MVeszpremi/M202_Solar_Tracker/data/image/3.jpg

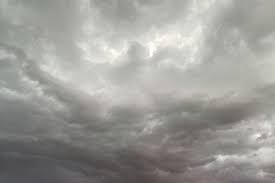
data/image/3.jpg
