MVeszpremi/M202_Solar_Tracker/data/image/7.jpg

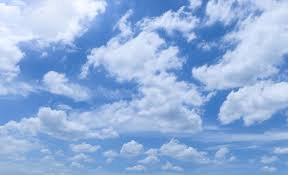
data/image/7.jpg
