MVeszpremi/M202_Solar_Tracker/data/image/8.jpg

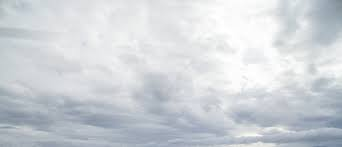
data/image/8.jpg
