MVeszpremi/M202_Solar_Tracker/data/image/10.jpg

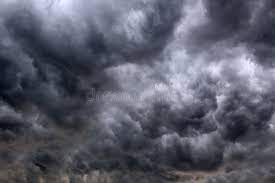
data/image/10.jpg
