MVeszpremi/M202_Solar_Tracker/data/image/11.jpg

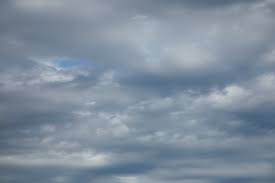
data/image/11.jpg
