MVeszpremi/M202_Solar_Tracker/data/image/12.jpg

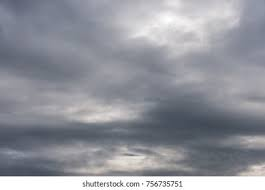
data/image/12.jpg
