MVeszpremi/M202_Solar_Tracker/data/image/13.jpg

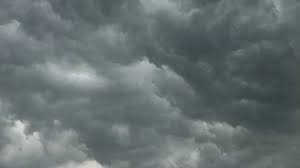
data/image/13.jpg
