MVeszpremi/M202_Solar_Tracker/data/image/14.jpg

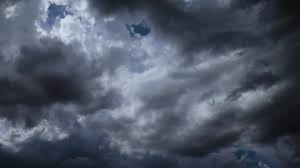
data/image/14.jpg
