MVeszpremi/M202_Solar_Tracker/data/image/15.jpg

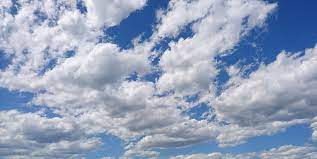
data/image/15.jpg
