MVeszpremi/M202_Solar_Tracker/data/image/16.jpg

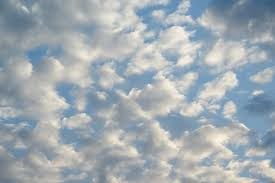
data/image/16.jpg
