MVeszpremi/M202_Solar_Tracker/data/image/17.jpg

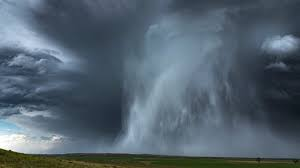
data/image/17.jpg
