MVeszpremi/M202_Solar_Tracker/data/image/19.jpg

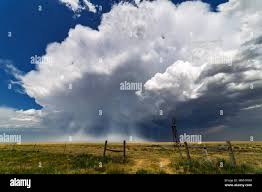
data/image/19.jpg
