MVeszpremi/M202_Solar_Tracker/data/image/20.jpg

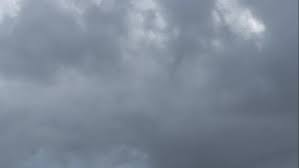
data/image/20.jpg
