MVeszpremi/M202_Solar_Tracker/data/image/sunny1.jpg

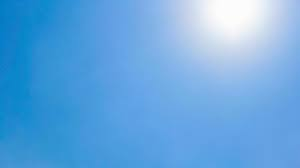
data/image/sunny1.jpg
