MVeszpremi/M202_Solar_Tracker/data/image/sunny2.jpg

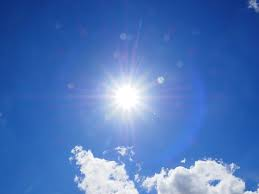
data/image/sunny2.jpg
