MVeszpremi/M202_Solar_Tracker/data/image/sunny4.jpg

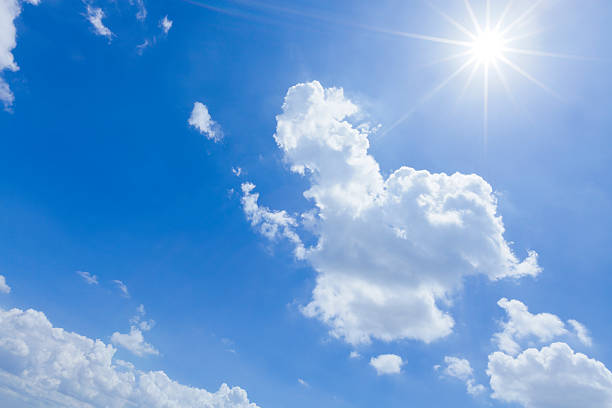
data/image/sunny4.jpg
