MVeszpremi/M202_Solar_Tracker/data/image/sunny5.jpg

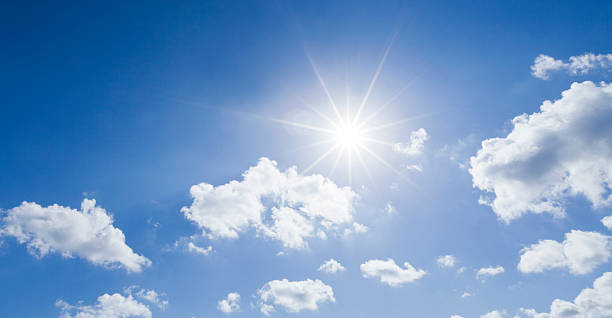
data/image/sunny5.jpg
