MVeszpremi/M202_Solar_Tracker/data/image/sunny6.jpg

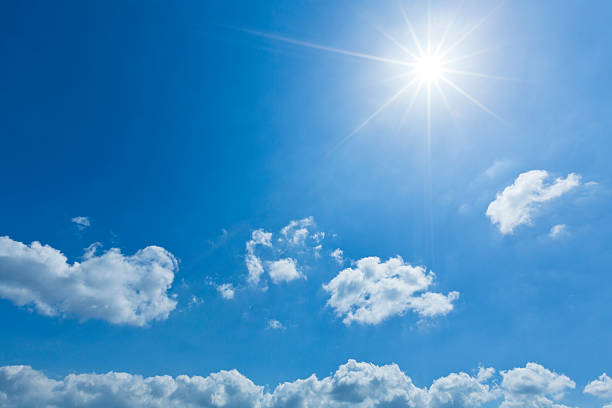
data/image/sunny6.jpg
