MVeszpremi/M202_Solar_Tracker/data/image/sunny7.jpg

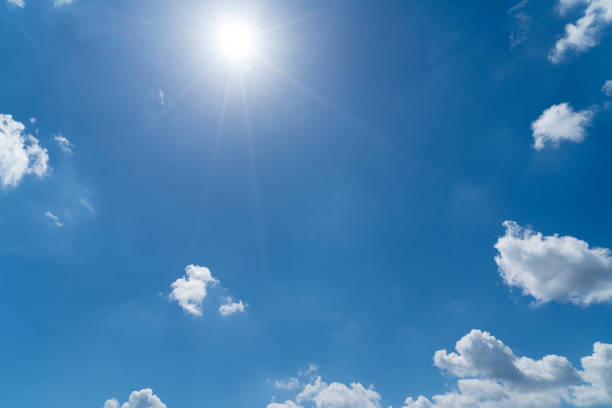
data/image/sunny7.jpg
