MVeszpremi/M202_Solar_Tracker/data/image/sunny8.jpg

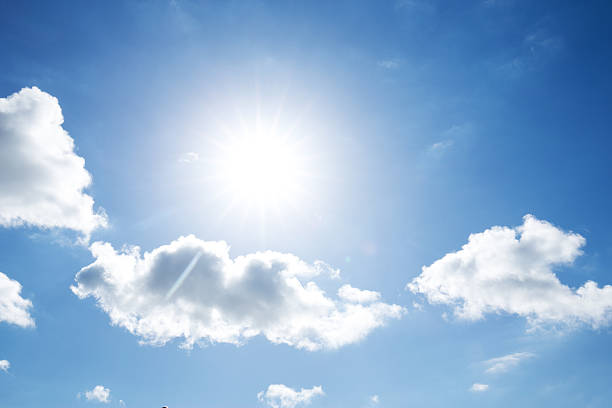
data/image/sunny8.jpg
