MVeszpremi/M202_Solar_Tracker/data/image/sunny9.jpg

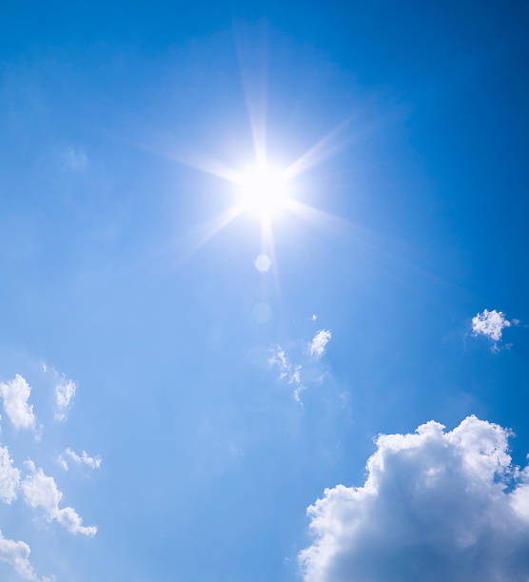
data/image/sunny9.jpg
