MVeszpremi/M202_Solar_Tracker/data/image/sunny10.jpg

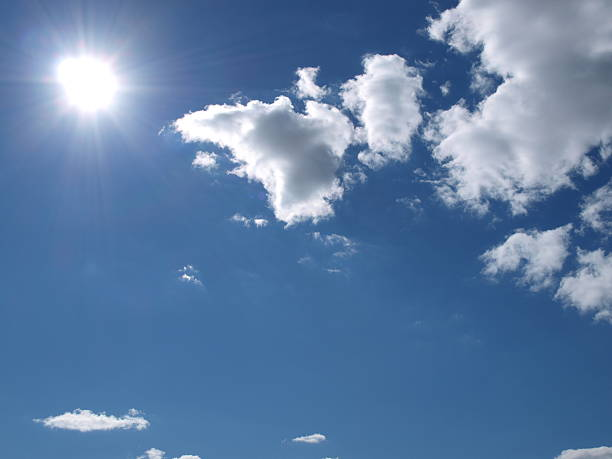
data/image/sunny10.jpg
