MVeszpremi/M202_Solar_Tracker/data/image/sunny11.jpg

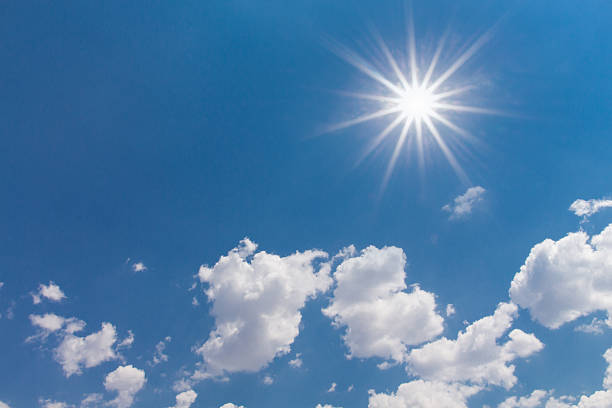
data/image/sunny11.jpg
