MVeszpremi/M202_Solar_Tracker/data/image/sunny12.jpg

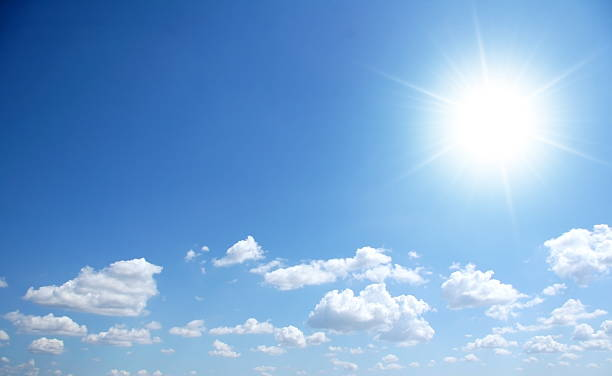
data/image/sunny12.jpg
