MVeszpremi/M202_Solar_Tracker/data/image/sunny13.jpg

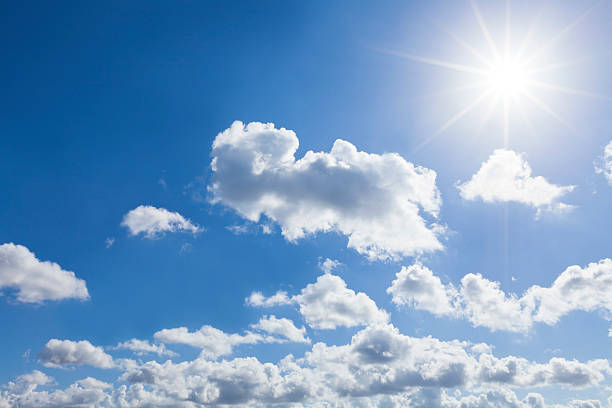
data/image/sunny13.jpg
