MVeszpremi/M202_Solar_Tracker/data/image/sunny15.jpg

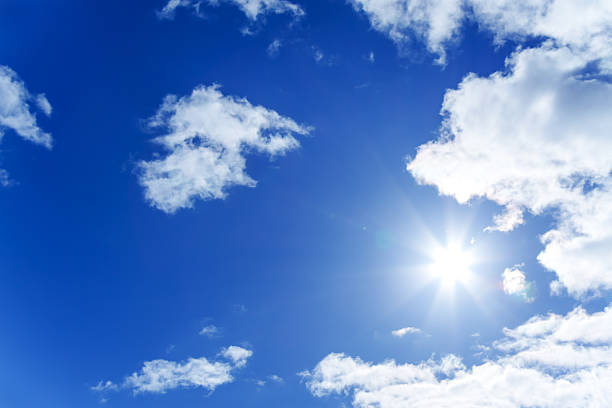
data/image/sunny15.jpg
