MVeszpremi/M202_Solar_Tracker/data/image/sunny.jpg

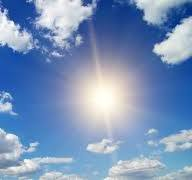
data/image/sunny.jpg
