MVeszpremi/M202_Solar_Tracker/software/Calibration_Codes_Images/frame-0.0.png

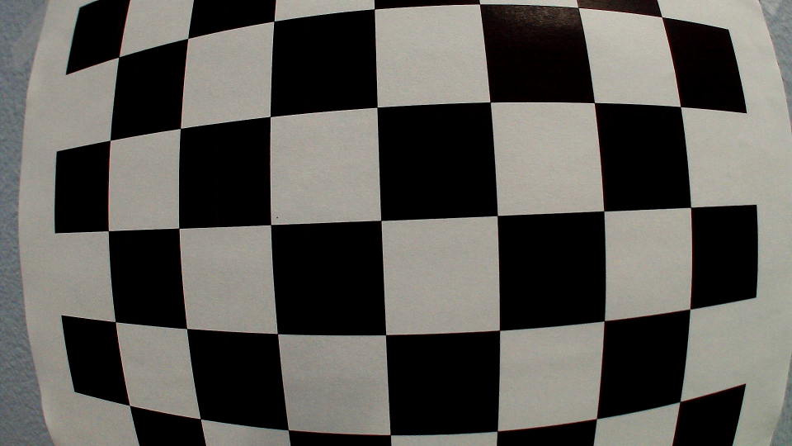
software/Calibration_Codes_Images/frame-0.0.png
